DigitalRealitiesLab/AirResMask/Electronics/KiCAD/RespiratorIF_Board_3D_Back.jpg

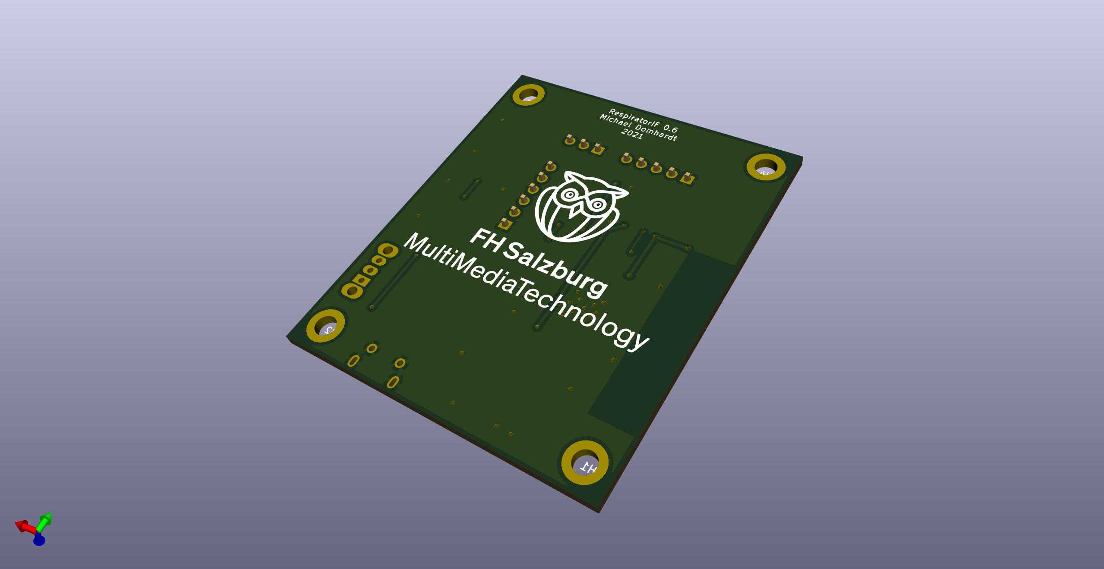
Electronics/KiCAD/RespiratorIF_Board_3D_Back.jpg
