DigitalRealitiesLab/AirResMask/Software/UnitySample/Assets/Scenes/Sample/Lightmap-0_comp_dir.png

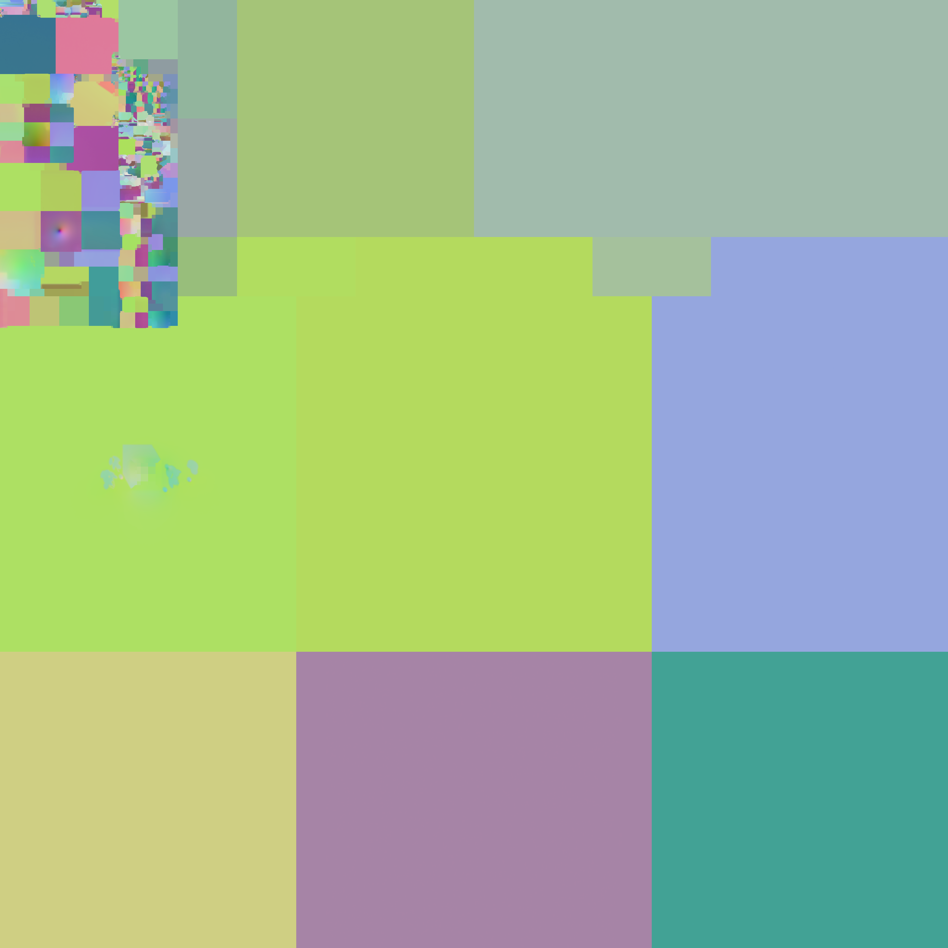
Software/UnitySample/Assets/Scenes/Sample/Lightmap-0_comp_dir.png
