DigitalRealitiesLab/AirResMask/CAD/3D Print/Plug Cover.stl

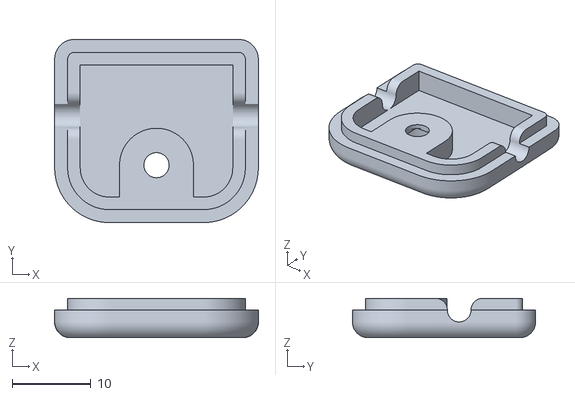
[picture p20: CAD file, 2021-11-24]
CAD/3D Print/Plug Cover.stl
25.9 x 23.3 x 5.00
