DigitalRealitiesLab/AirResMask/CAD/3D Print/gapWidth variable/Air Duct 2.6828.stl

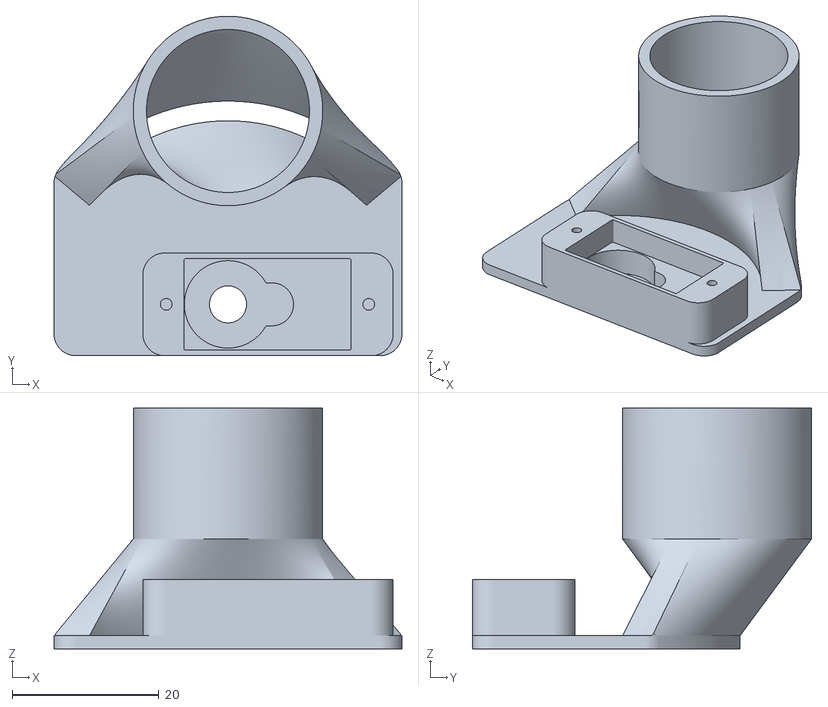
[picture p21: CAD file, 2021-11-24]
CAD/3D Print/gapWidth variable/Air Duct 2.6828.stl
47.4 x 46.2 x 32.8
