DigitalRealitiesLab/AirResMask/CAD/3D Print/Plug Body.stl

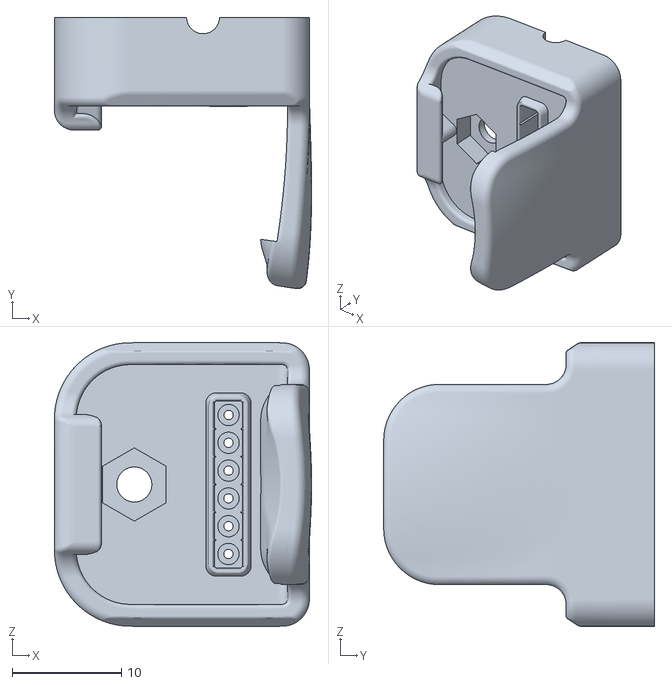
[picture p22: CAD file, 2021-11-24]
CAD/3D Print/Plug Body.stl
23.5 x 24.8 x 25.9
