DigitalRealitiesLab/AirResMask/CAD/3D Print/gapWidth variable/Air Restrictor Clearance 4.1828.stl

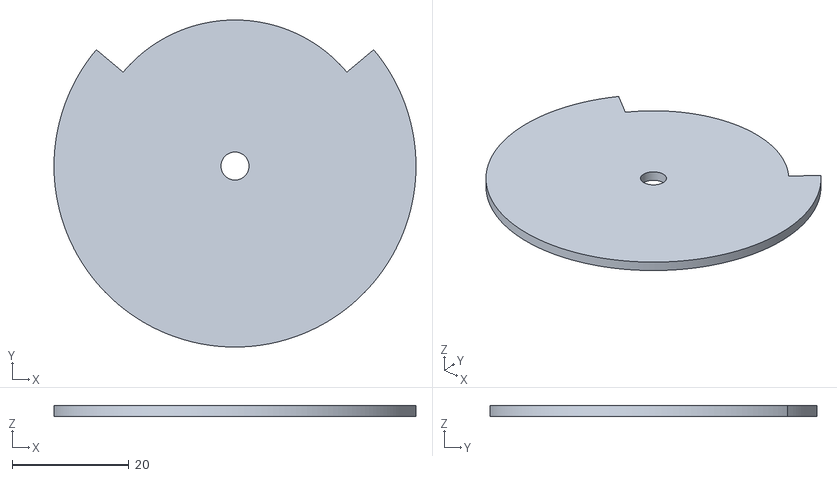
[picture p23: CAD file, 2021-11-24]
CAD/3D Print/gapWidth variable/Air Restrictor Clearance 4.1828.stl
62.0 x 56.0 x 1.80
