DigitalRealitiesLab/AirResMask/CAD/3D Print/Plug.3mf

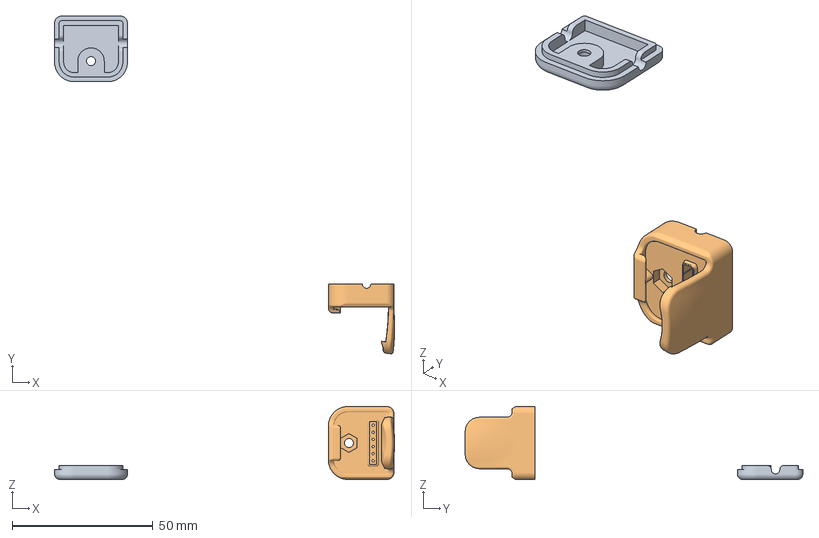
[picture p24: CAD file, 2021-11-24]
CAD/3D Print/Plug.3mf
120.8 x 120.0 x 25.9 mm
Plug Cover.stl
Plug Body.stl
