DigitalRealitiesLab/AirResMask/CAD/3D Print/gapWidth variable/Air Restrictor Clearance 3.1828.stl

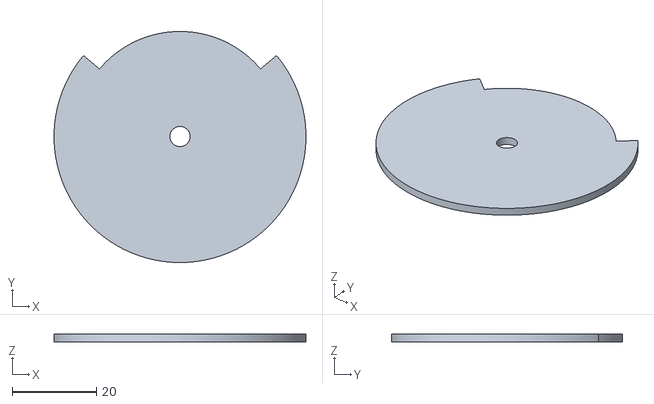
[picture p25: CAD file, 2021-11-24]
CAD/3D Print/gapWidth variable/Air Restrictor Clearance 3.1828.stl
60.0 x 55.0 x 1.80
