DigitalRealitiesLab/AirResMask/CAD/3D Print/gapWidth variable/Air Restrictor Clearance 2.1828.stl

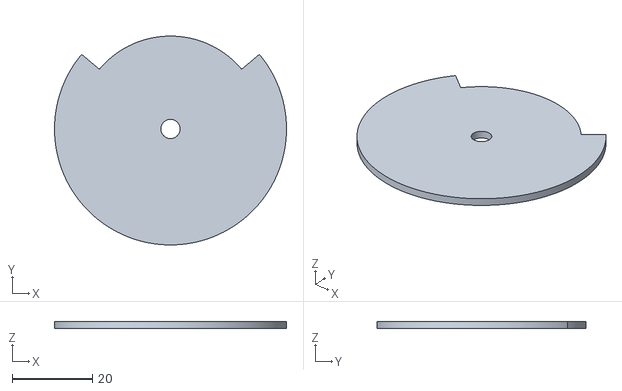
[picture p26: CAD file, 2021-11-24]
CAD/3D Print/gapWidth variable/Air Restrictor Clearance 2.1828.stl
58.0 x 52.2 x 1.80
