DigitalRealitiesLab/AirResMask/CAD/3D Print/gapWidth variable/Air Duct 4.1828.stl

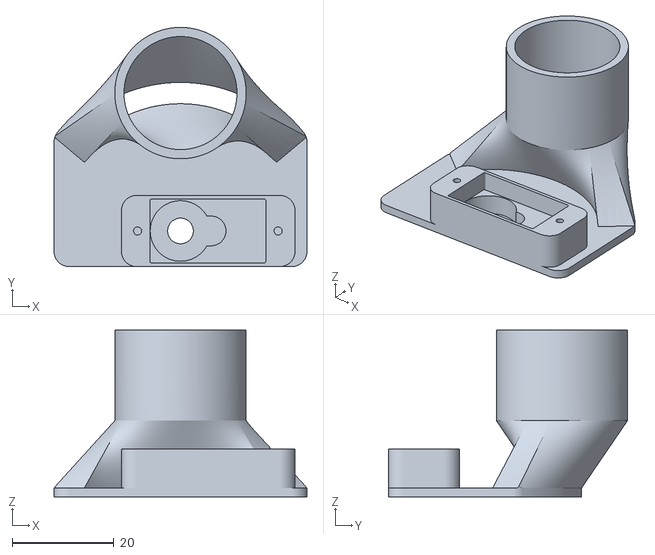
[picture p27: CAD file, 2021-11-24]
CAD/3D Print/gapWidth variable/Air Duct 4.1828.stl
49.7 x 47.0 x 32.8
